simonescaccia/IoTProject/deliveries/2st-delivery/graph/ack_quantity.png

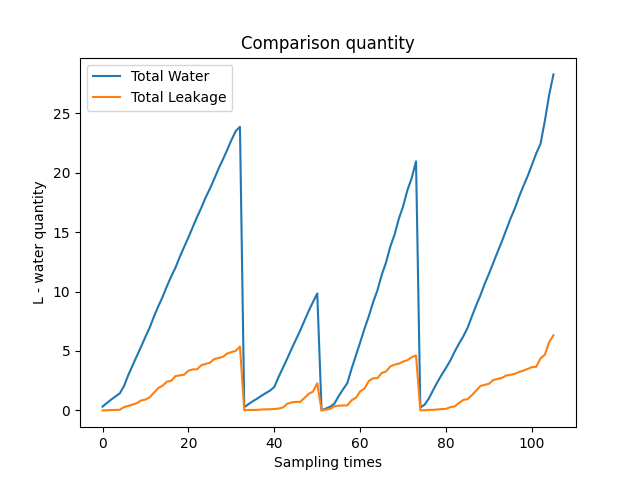
deliveries/2st-delivery/graph/ack_quantity.png
