simonescaccia/IoTProject/deliveries/2st-delivery/graph/bathroom_flow.png

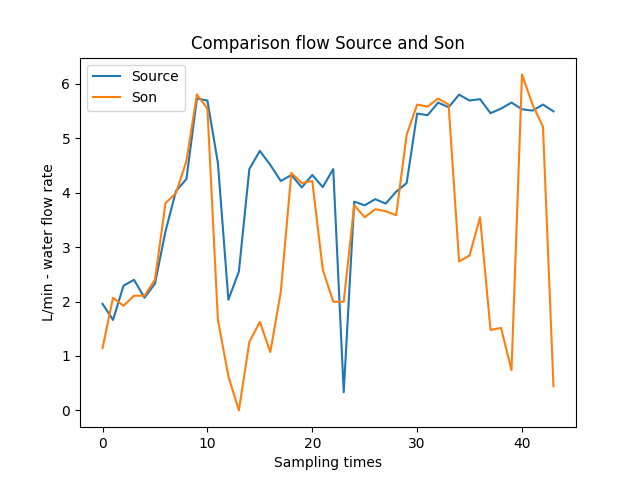
deliveries/2st-delivery/graph/bathroom_flow.png
