simonescaccia/IoTProject/deliveries/2st-delivery/graph/bathroom_quantity.png

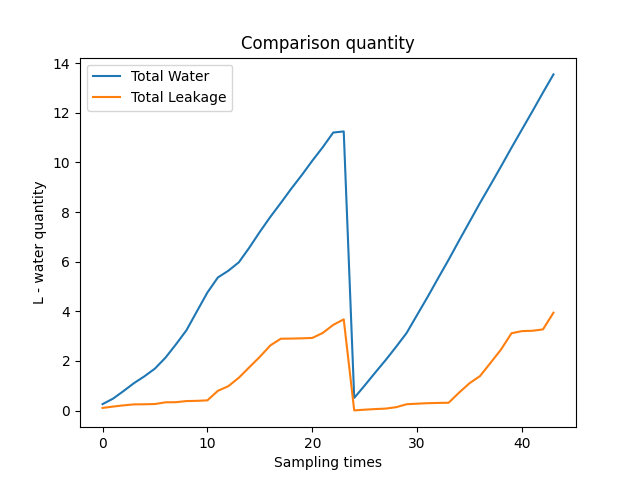
deliveries/2st-delivery/graph/bathroom_quantity.png
