simonescaccia/IoTProject/deliveries/2st-delivery/graph/handshake_flow.png

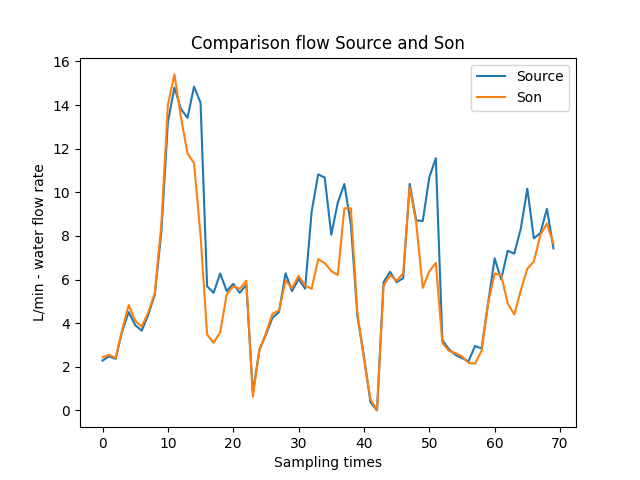
deliveries/2st-delivery/graph/handshake_flow.png
