simonescaccia/IoTProject/deliveries/2st-delivery/graph/handshake_quantity.png

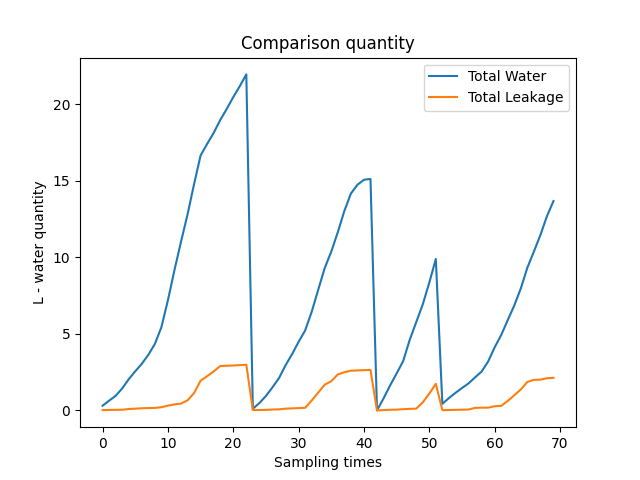
deliveries/2st-delivery/graph/handshake_quantity.png
