simonescaccia/IoTProject/deliveries/2st-delivery/graph/syncAck_flow.png

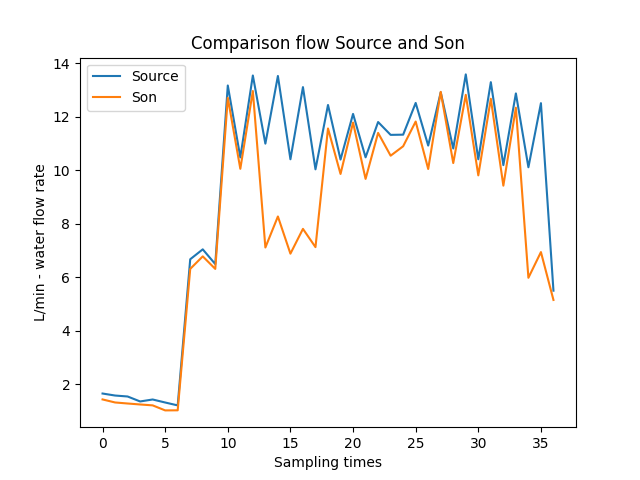
deliveries/2st-delivery/graph/syncAck_flow.png
