simonescaccia/IoTProject/deliveries/2st-delivery/graph/syncAck_quantity.png

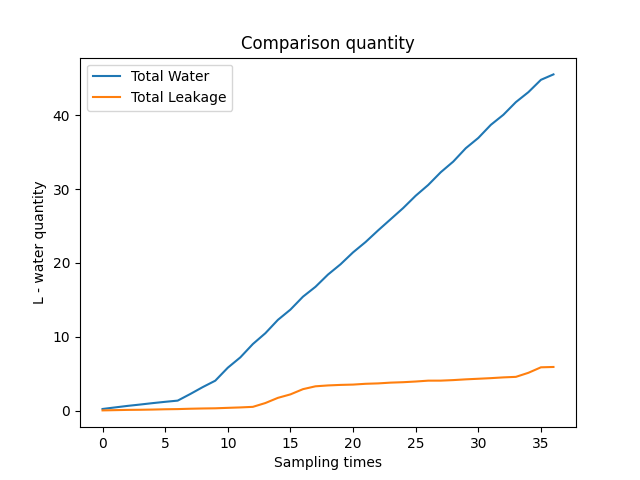
deliveries/2st-delivery/graph/syncAck_quantity.png
