simonescaccia/IoTProject/deliveries/2st-delivery/images/field_alternative.jpg

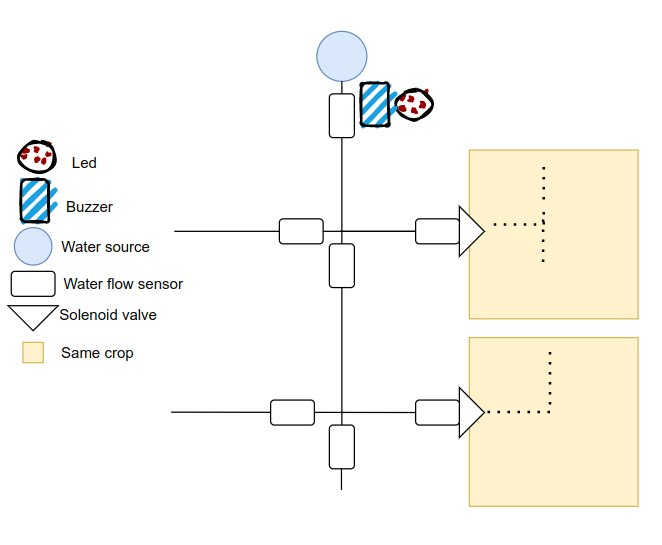
deliveries/2st-delivery/images/field_alternative.jpg
