simonescaccia/IoTProject/energy_consumption/5.1-Lora-two-send.png

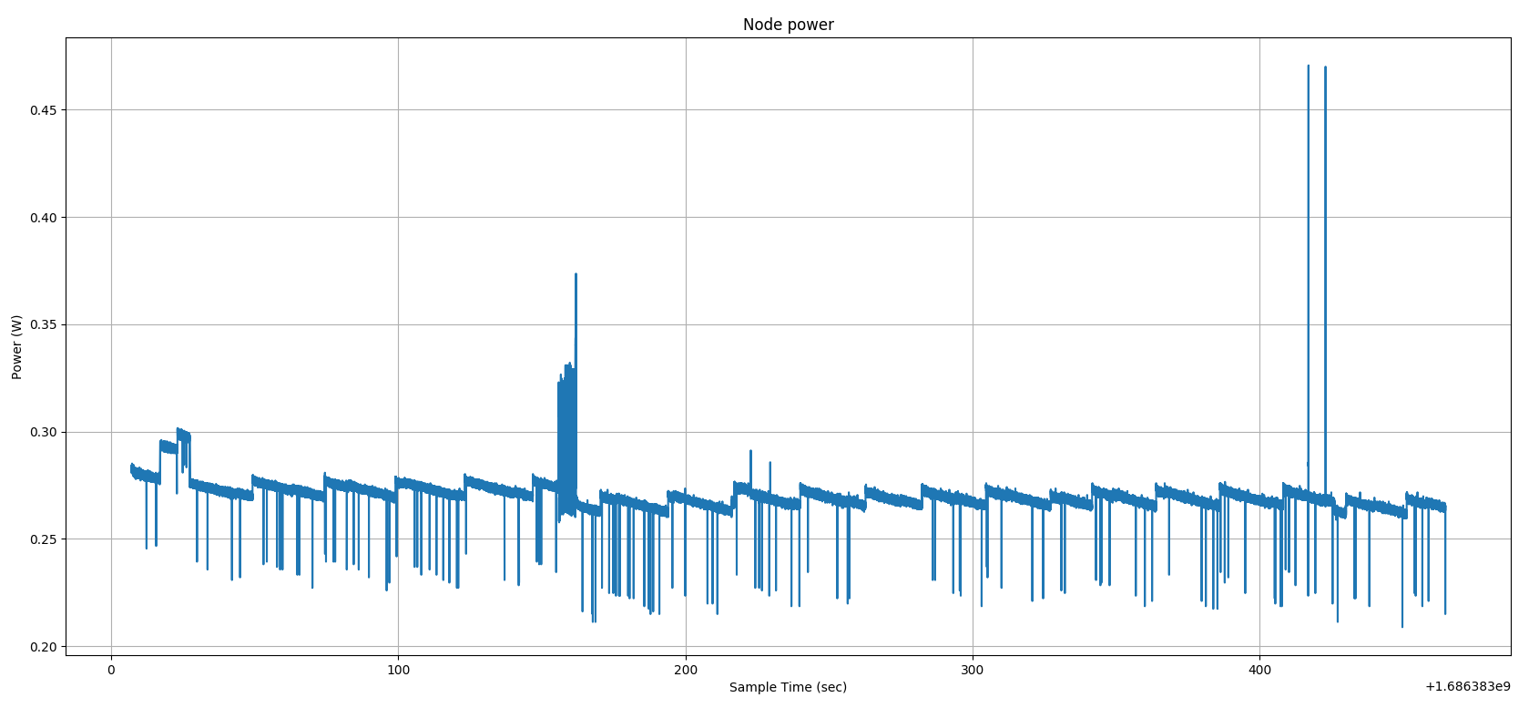
energy_consumption/5.1-Lora-two-send.png
