simonescaccia/IoTProject/energy_consumption/5.2-Lora-p2p-one-send-zoom.png

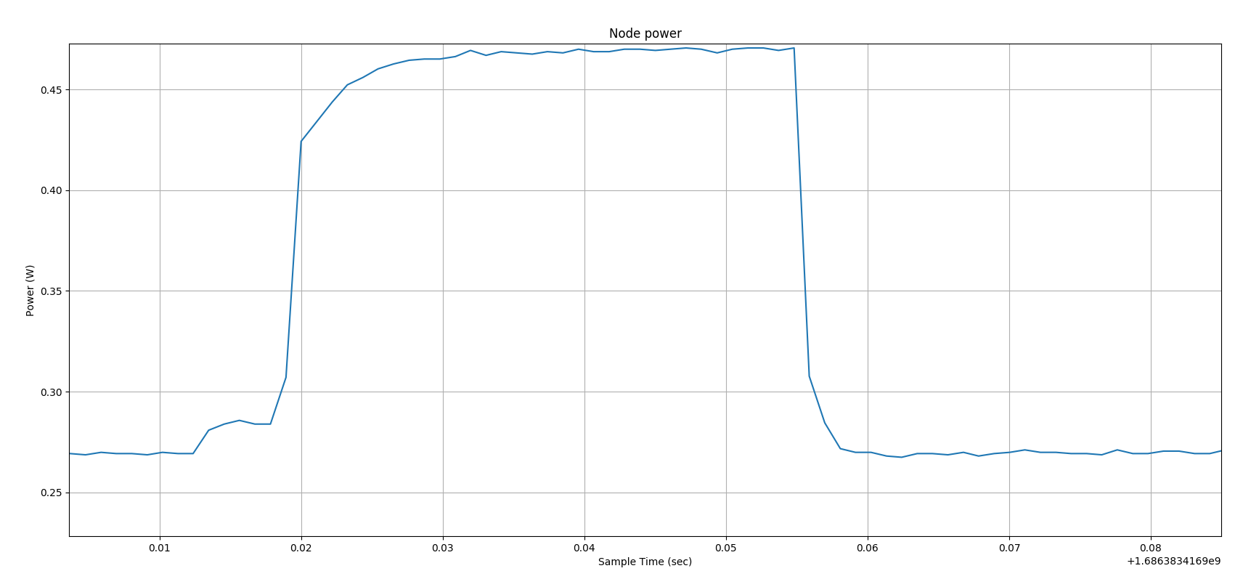
energy_consumption/5.2-Lora-p2p-one-send-zoom.png
