simonescaccia/IoTProject/energy_consumption/6.1-Lora-p2p-BRANCH-leakage.png

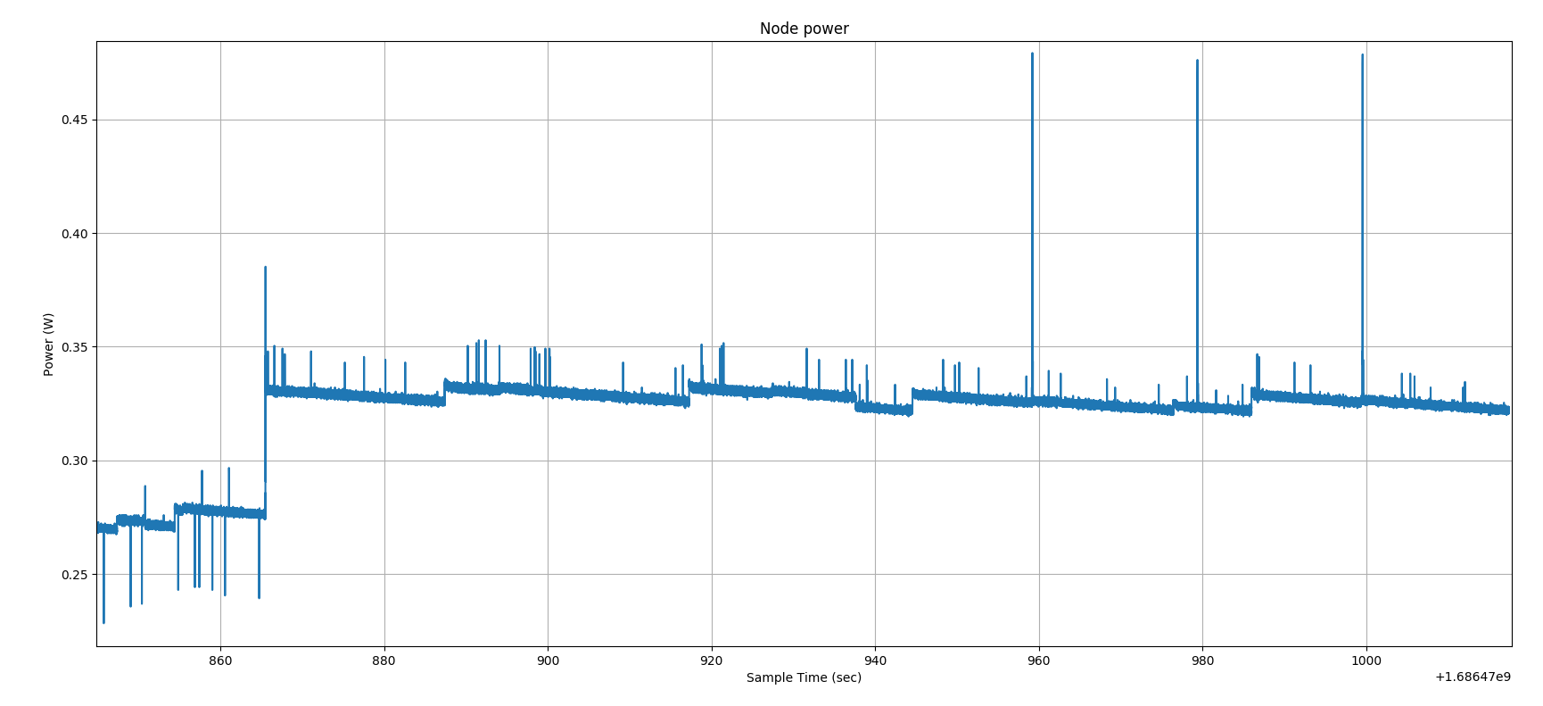
energy_consumption/6.1-Lora-p2p-BRANCH-leakage.png
