simonescaccia/IoTProject/energy_consumption/6.2-Lora-p2p-BRANCH-leakage-zoom-dataReception-before-sending.png

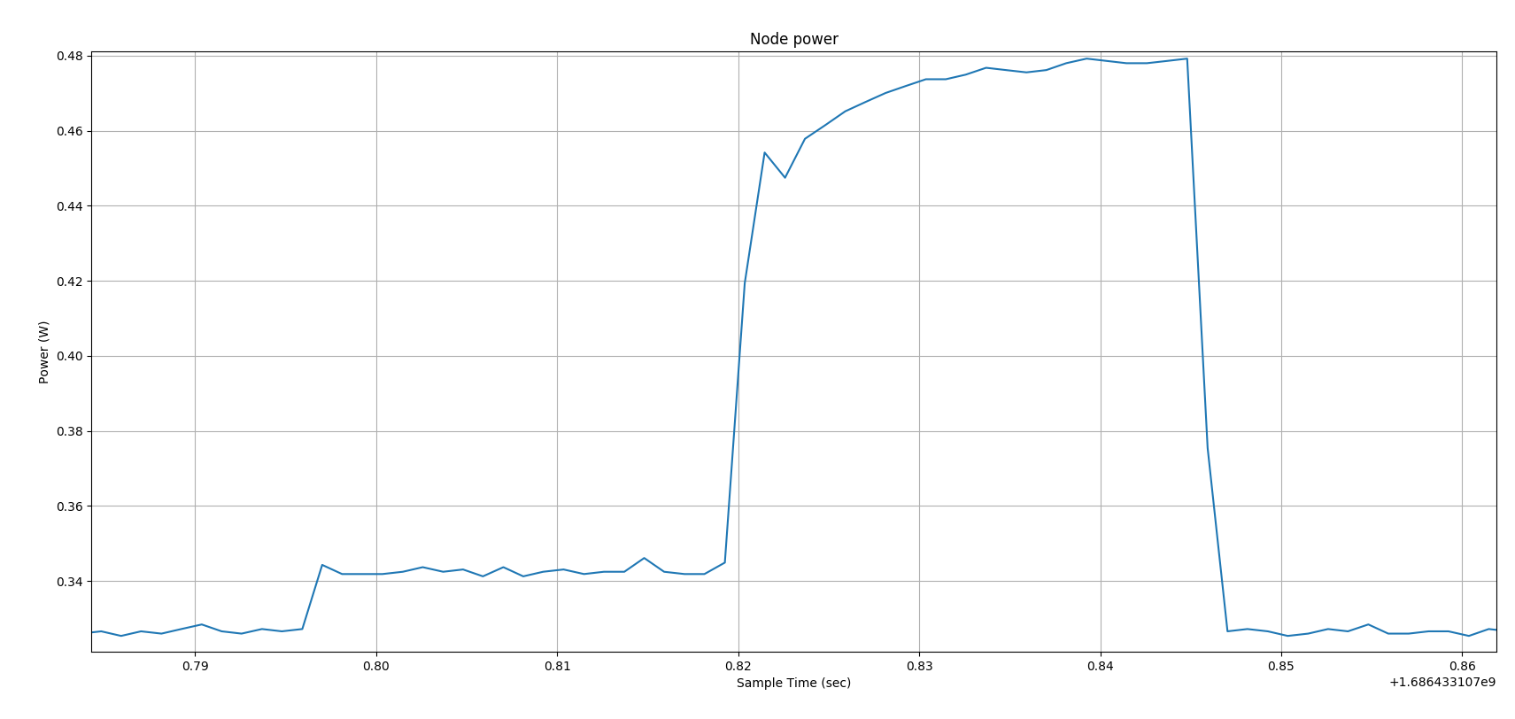
energy_consumption/6.2-Lora-p2p-BRANCH-leakage-zoom-dataReception-before-sending.png
