simonescaccia/IoTProject/graph/error.png

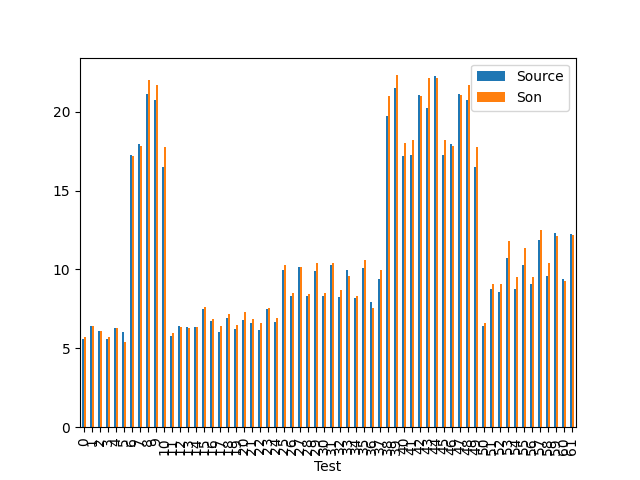
graph/error.png
