simonescaccia/IoTProject/graph/syncAck_close_end_pipeline.png

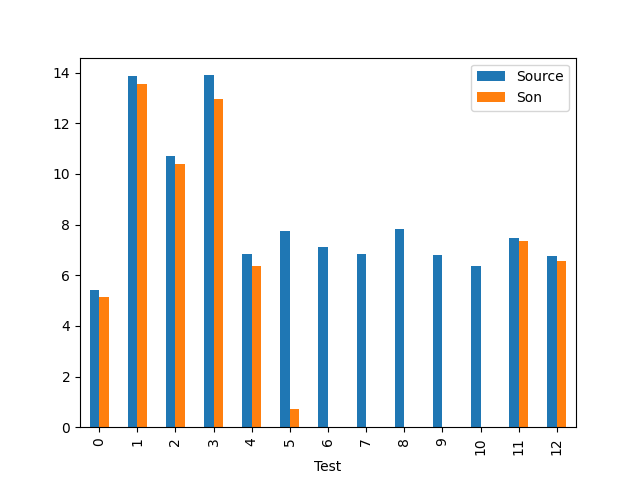
graph/syncAck_close_end_pipeline.png
