simonescaccia/IoTProject/images/handshake_time1.png

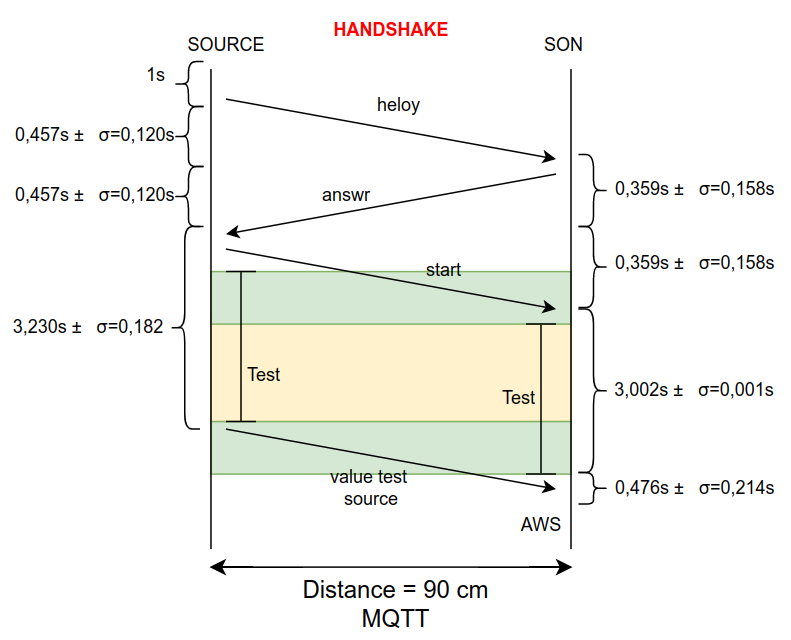
images/handshake_time1.png
