simonescaccia/IoTProject/images/Simulation-Page-1.drawio.png

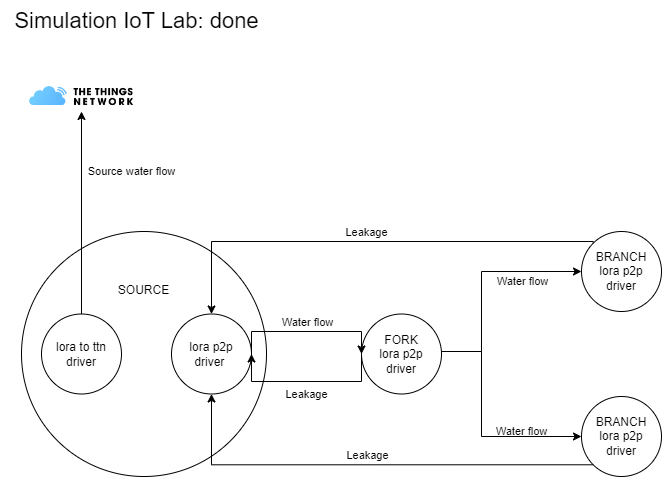
images/Simulation-Page-1.drawio.png
