simonescaccia/IoTProject/images/Simulation-Page-2.drawio.png

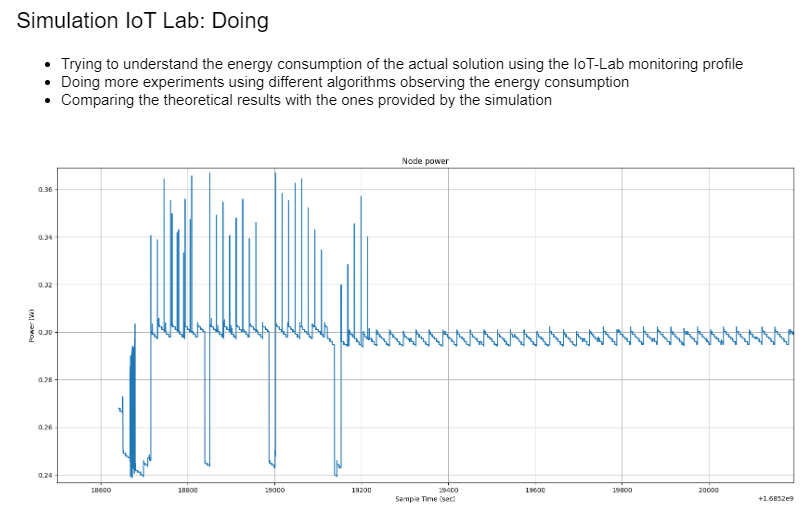
images/Simulation-Page-2.drawio.png
