simonescaccia/IoTProject/images/Simulation-Page-3.drawio.png

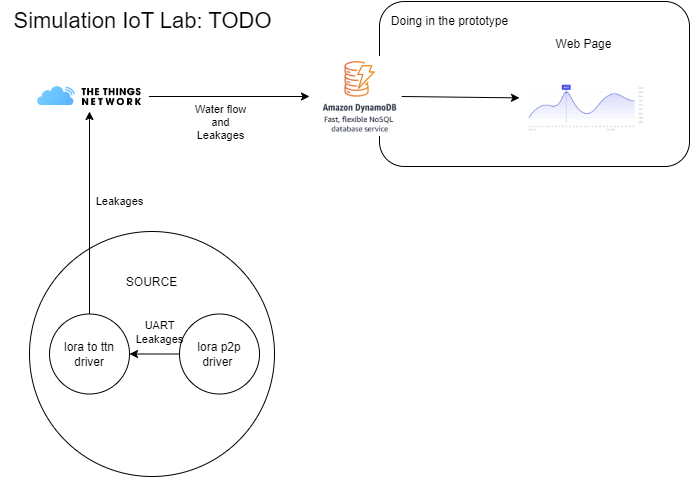
images/Simulation-Page-3.drawio.png
