simonescaccia/IoTProject/images/syncAck_time1.png

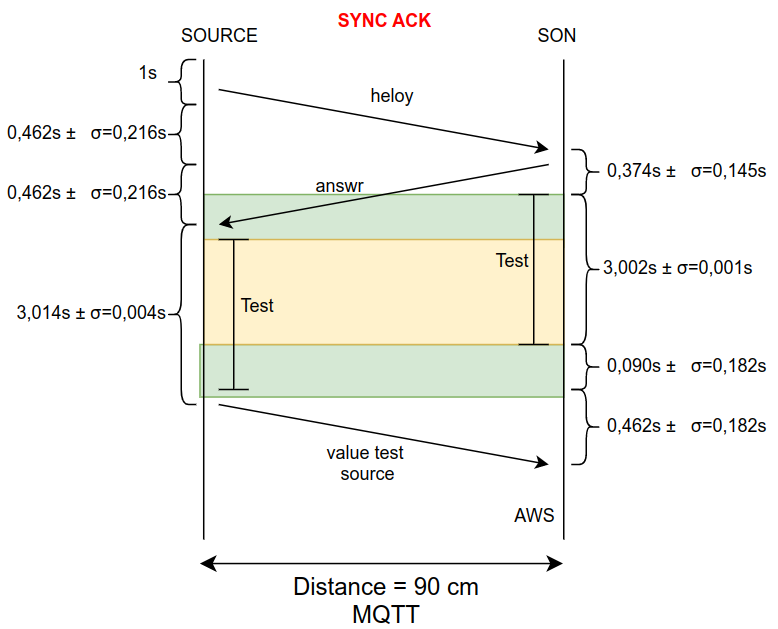
images/syncAck_time1.png
