simonescaccia/IoTProject/graph/ack_test2.png

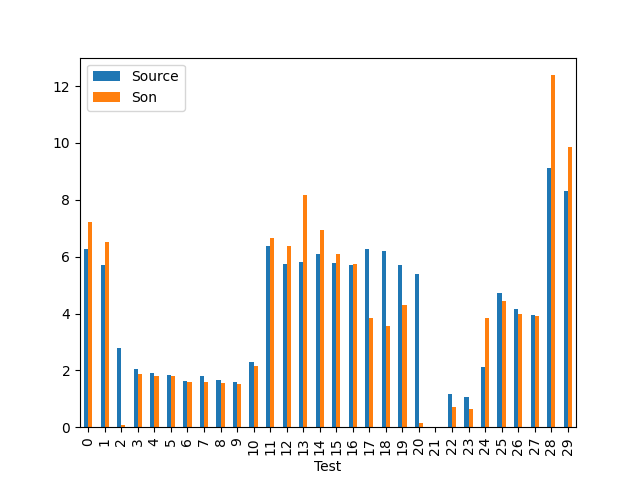
graph/ack_test2.png
